YamiYukiSenpai/EZTracker/Documentation/EZ_Tracker_Schedule.PNG

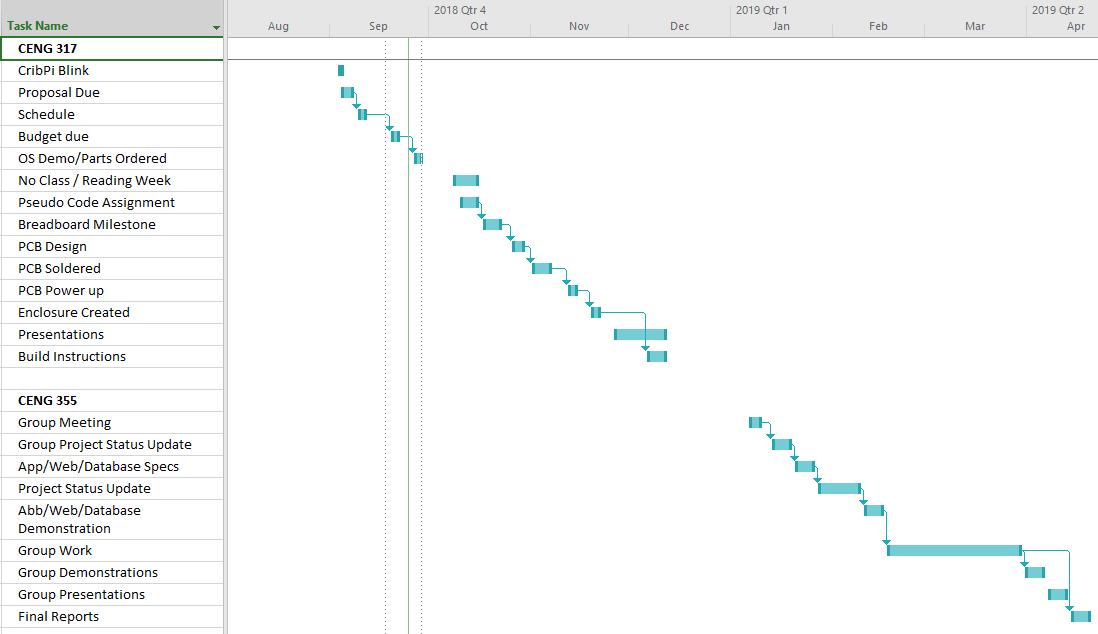
Documentation/EZ_Tracker_Schedule.PNG
