YamiYukiSenpai/EZTracker/Documentation/Pictures/pcb_sensors.jpg

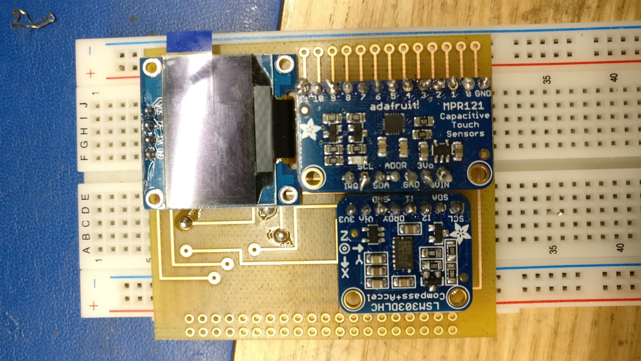
Documentation/Pictures/pcb_sensors.jpg
