YamiYukiSenpai/EZTracker/Documentation/Pictures/project_case.jpg

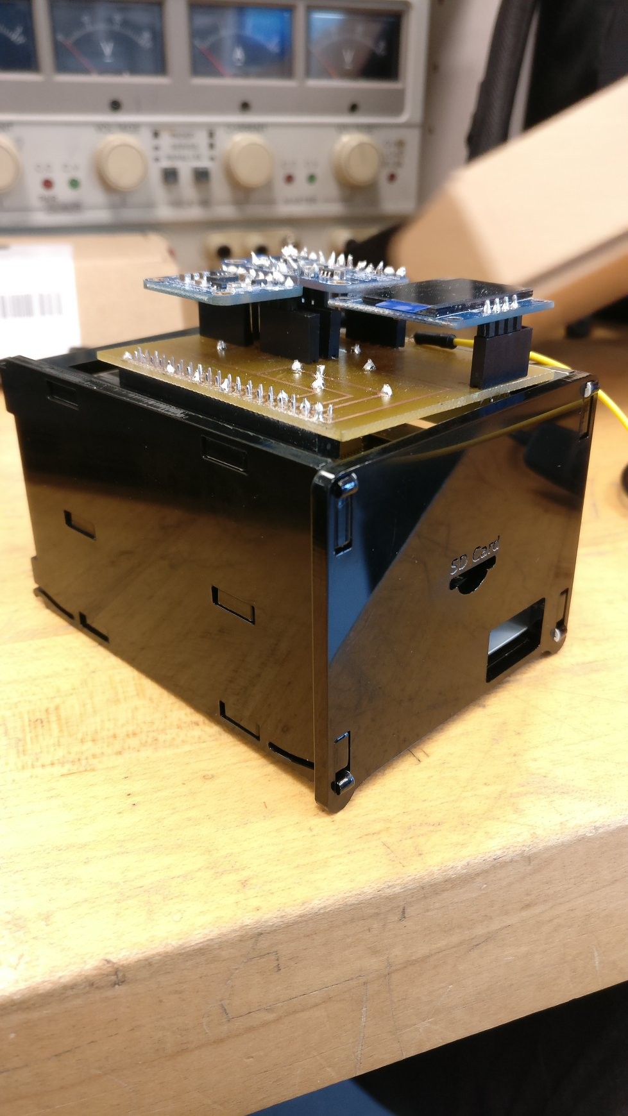
Documentation/Pictures/project_case.jpg
