YamiYukiSenpai/EZTracker/PCB Files/EZ_v2_Final.png

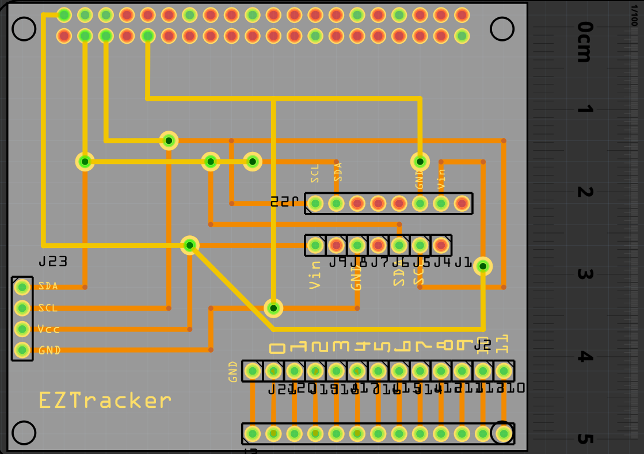
PCB Files/EZ_v2_Final.png
