YamiYukiSenpai/EZTracker/Software/Login v3/background2.jpg

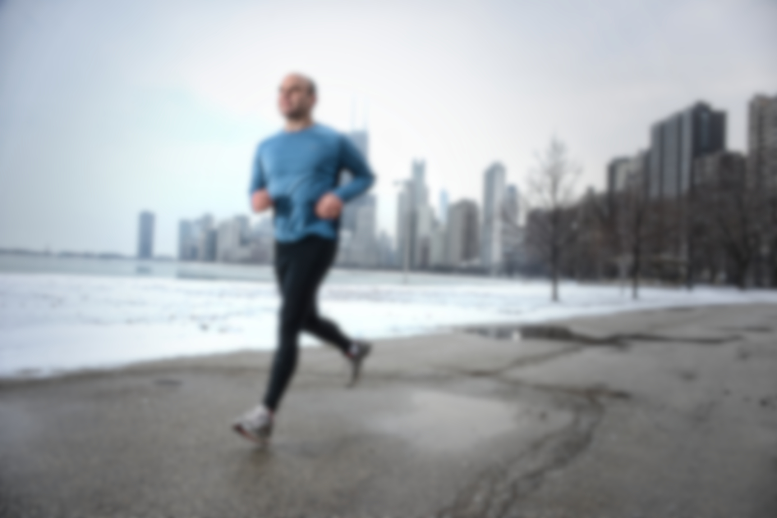
Software/Login v3/background2.jpg
