YamiYukiSenpai/EZTracker/Documentation/Pictures/caseResult2.png

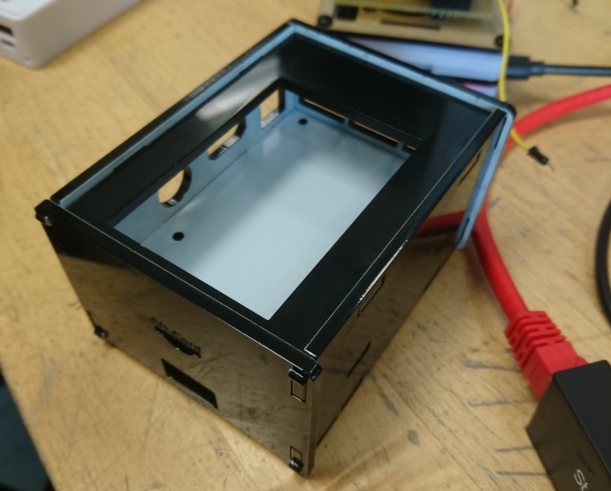
Documentation/Pictures/caseResult2.png
